tcfh2003/Virtex-6-ML602-ADCDAC-PCB/Schematic_and_PCB_Photos/rev1.1/ML605_LPC_Board_wADC_DAC conv 1.png

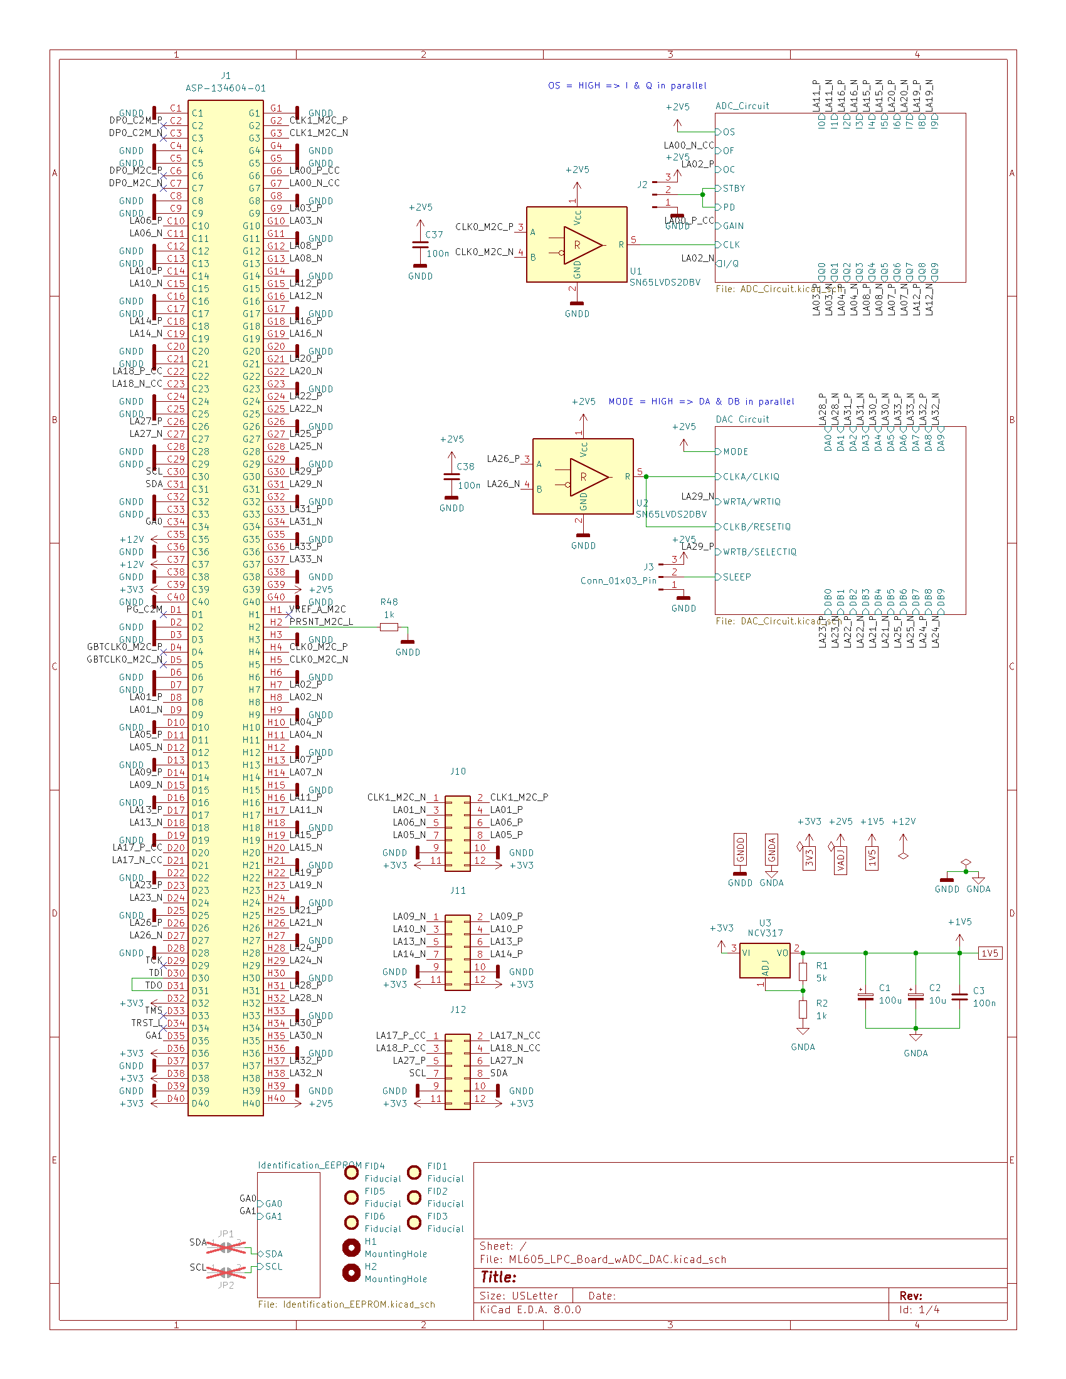
Schematic_and_PCB_Photos/rev1.1/ML605_LPC_Board_wADC_DAC conv 1.png
