tcfh2003/Virtex-6-ML602-ADCDAC-PCB/DAC_differential_amp.asc

C1: cap; 200µ
C2: cap; 10µ
I1: current; SINE(10m 10m 100MEG 0 0 0)
I2: current; SINE(10m 10m 100MEG 0 0 180)
R1: res; 600
R2: res; 600
R3: res; 600
R4: res; 600
R5: res; 50
R6: res; 50
R7: res; 50
R8: res; 5k
R9: res; 1k
U2: UniversalOpAmp2; Avol=1Meg GBW=400Meg Slew=1800Meg; Ilimit=75m Rail=0 Vos=0
U3: LM317_TRANS
V1: voltage; 3.3
Named nets: VCC, 0
.tran 50n
